ehuang222/ergogen-keeb/outputs/outlines/keycaps.dxf

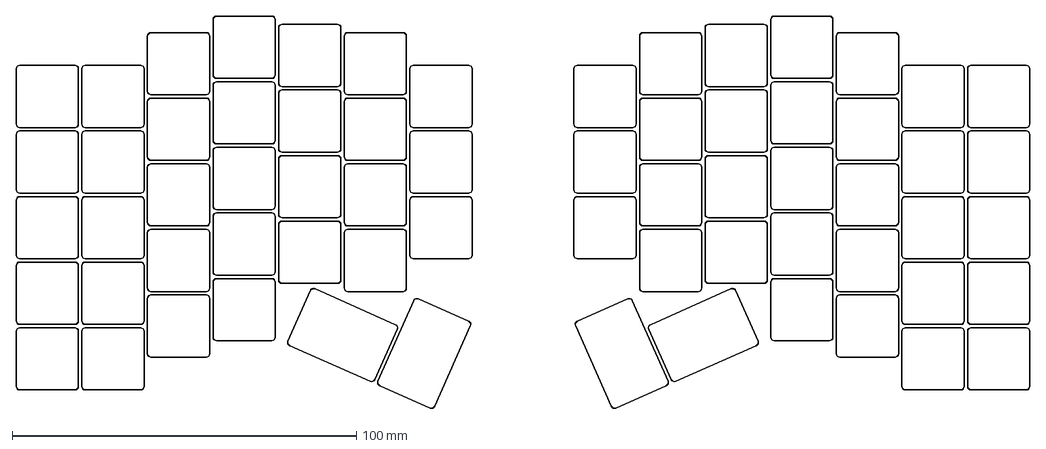
[picture p28: CAD file, 2026-08-02]
outputs/outlines/keycaps.dxf
294.3 x 114.0 mm
