ehuang222/ergogen-keeb/outputs/outlines/plate.dxf

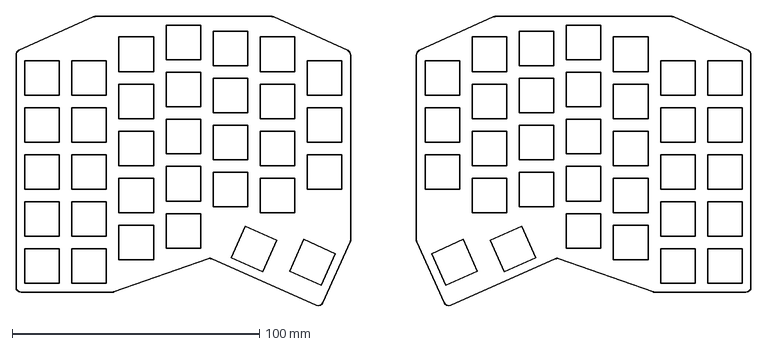
[picture p29: CAD file, 2026-08-02]
outputs/outlines/plate.dxf
297.3 x 117.3 mm
