ehuang222/ergogen-keeb/outputs/outlines/plate_left.dxf

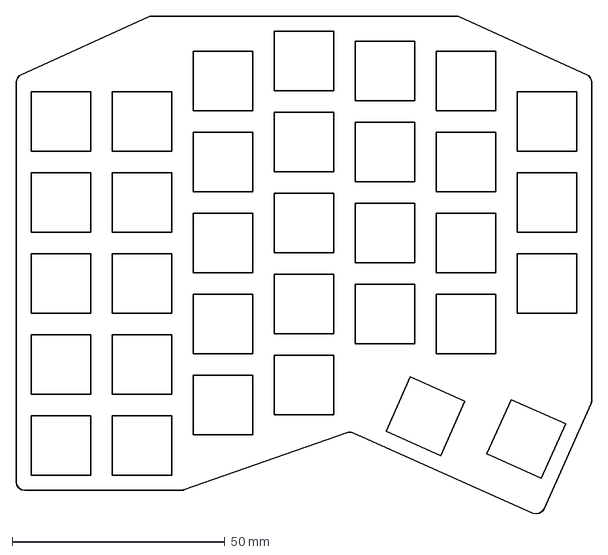
[picture p30: CAD file, 2026-08-02]
outputs/outlines/plate_left.dxf
135.4 x 117.3 mm
